fabi1609/Nixie_moch/SW/Core/Inc/settings.h

/*
 * settings.h
 *
 *  Created on: 27.02.2021
 *      Author: mochf
 */

#ifndef INC_SETTINGS_H_
#define INC_SETTINGS_H_

#define REBOOT_H 	3u
#define REBOOT_M	0u

#define DAC_TARGET 	2650 //2940 approx. 160V   2670=145V   4095 -> 223V

#endif /* INC_SETTINGS_H_ */
