fabi1609/Nixie_moch/SW/Core/Inc/boost.h

/*
 * boost.h
 *
 *  Created on: Oct 29, 2019
 *      Author: Fabian
 */

#ifndef INC_BOOST_H_
#define INC_BOOST_H_

#include "stm32g0xx_hal.h"
#include "stm32g0xx_ll_system.h"

void boost_op();

#endif /* INC_BOOST_H_ */
